eduardofv/virtual_wall/3d/led padder.FCStd

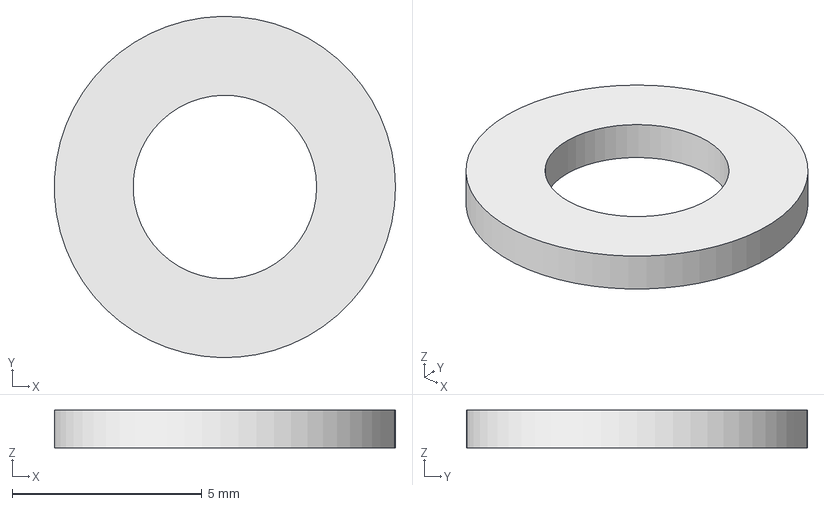
[picture p10: CAD file, 2022-07-13]
3d/led padder.FCStd
8.99 x 9.00 x 1.00 mm
