eduardofv/virtual_wall/3d/prueba_caja_tornillo.stl

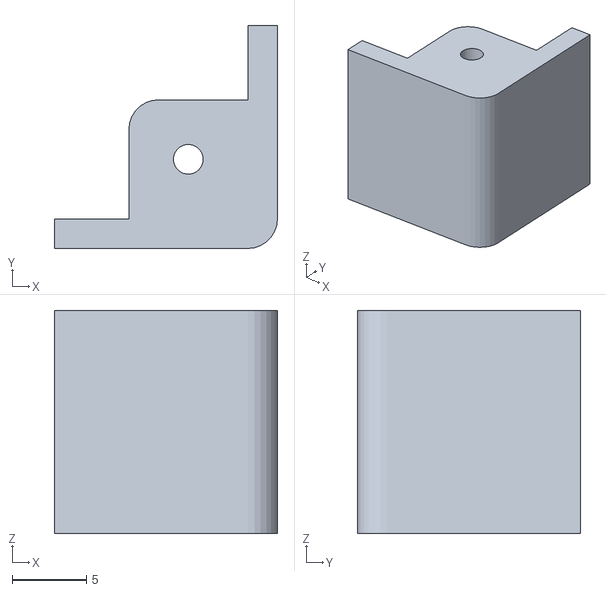
[picture p11: CAD file, 2022-07-13]
3d/prueba_caja_tornillo.stl
15.0 x 15.0 x 15.0
